KevTheKoiFishy/LMPK-362-Project/src/sd_sdcard.c

#include <stdio.h>
#include <stdlib.h>
#include <string.h>
#include <errno.h>
#include "pico/stdlib.h"

#include "sd_ff.h"
#include "sd_diskio.h"
#include "sd_sdcard.h"
#include "sd_uart.h"
#include "sd_audio.h"

#include "hardware/watchdog.h"
#include "watchdog.c"

// Just because i fw it
int _read(__unused int handle, char *buffer, int length);

FATFS fs_storage; // Global file system object
const char *month_name[] = {
    [1] = "Jan",
    [2] = "Feb",
    [3] = "Mar",
    [4] = "Apr",
    [5] = "May",
    [6] = "Jun",
    [7] = "Jul",
    [8] = "Aug",
    [9] = "Sep",
    [10] = "Oct",
    [11] = "Nov",
    [12] = "Dec",
};
typedef union {
    struct {
        unsigned int bisecond:5; // seconds divided by 2
        unsigned int minute:6;
        unsigned int hour:5;
        unsigned int day:5;
        unsigned int month:4;
        unsigned int year:7;
    };
} fattime_t;

// Current time in the FAT file system format.
static fattime_t fattime;

void set_fattime(int year, int month, int day, int hour, int minute, int second)
{
    fattime_t newtime;
    newtime.year = year - 1980;
    newtime.month = month;
    newtime.day = day;
    newtime.hour = hour;
    newtime.minute = minute;
    newtime.bisecond = second/2;
    int len = sizeof newtime;
    memcpy(&fattime, &newtime, len);
}

void advance_fattime(void)
{
    fattime_t newtime = fattime;
    newtime.bisecond += 1;
    if (newtime.bisecond == 30) {
        newtime.bisecond = 0;
        newtime.minute += 1;
    }
    if (newtime.minute == 60) {
        newtime.minute = 0;
        newtime.hour += 1;
    }
    if (newtime.hour == 24) {
        newtime.hour = 0;
        newtime.day += 1;
    }
    if (newtime.month == 2) {
        if (newtime.day >= 29) {
            int year = newtime.year + 1980;
            if ((year % 1000) == 0) { // we have a leap day in 2000
                if (newtime.day > 29) {
                    newtime.day -= 28;
                    newtime.month = 3;
                }
            } else if ((year % 100) == 0) { // no leap day in 2100
                if (newtime.day > 28)
                newtime.day -= 27;
                newtime.month = 3;
            } else if ((year % 4) == 0) { // leap day for other mod 4 years
                if (newtime.day > 29) {
                    newtime.day -= 28;
                    newtime.month = 3;
                }
            }
        }
    } else if (newtime.month == 9 || newtime.month == 4 || newtime.month == 6 || newtime.month == 10) {
        if (newtime.day == 31) {
            newtime.day -= 30;
            newtime.month += 1;
        }
    } else {
        if (newtime.day == 0) { // cannot advance to 32
            newtime.day = 1;
            newtime.month += 1;
        }
    }
    if (newtime.month == 13) {
        newtime.month = 1;
        newtime.year += 1;
    }

    fattime = newtime;
}

uint32_t get_fattime(void)
{
    union FattimeUnion {
        fattime_t time;
        uint32_t value;
    };

    union FattimeUnion u;
    u.time = fattime;
    return u.value;
}

int to_int(char *start, char *end, int base)
{
    int n = 0;
    for( ; start != end; start++)
        n = n * base + (*start - '0');
    return n;
}

void print_error(FRESULT fr, const char *msg)
{
    const char *errs[] = {
            [FR_OK] = "Success",
            [FR_DISK_ERR] = "Hard error in low-level disk I/O layer",
            [FR_INT_ERR] = "Assertion failed",
            [FR_NOT_READY] = "Physical drive cannot work",
            [FR_NO_FILE] = "File not found",
            [FR_NO_PATH] = "Path not found",
            [FR_INVALID_NAME] = "Path name format invalid",
            [FR_DENIED] = "Permision denied",
            [FR_EXIST] = "Prohibited access",
            [FR_INVALID_OBJECT] = "File or directory object invalid",
            [FR_WRITE_PROTECTED] = "Physical drive is write-protected",
            [FR_INVALID_DRIVE] = "Logical drive number is invalid",
            [FR_NOT_ENABLED] = "Volume has no work area",
            [FR_NO_FILESYSTEM] = "Not a valid FAT volume",
            [FR_MKFS_ABORTED] = "f_mkfs aborted",
            [FR_TIMEOUT] = "Unable to obtain grant for object",
            [FR_LOCKED] = "File locked",
            [FR_NOT_ENOUGH_CORE] = "File name is too large",
            [FR_TOO_MANY_OPEN_FILES] = "Too many open files",
            [FR_INVALID_PARAMETER] = "Invalid parameter",
    };
    if (fr < 0 || fr >= sizeof errs / sizeof errs[0])
        printf("%s: Invalid error\n", msg);
    else
        printf("%s: %s\n", msg, errs[fr]);
}

void date(int argc, char *argv[])
{
    if (argc == 2) {
        char *d = argv[1];
        if (strlen(d) != 14) {
            printf("Date format: YYYYMMDDHHMMSS\n");
            return;
        }
        for(int i=0; i<14; i++)
            if (d[i] < '0' || d[i] > '9') {
                printf("Date format: YYYMMDDHHMMSS\n");
                return;
            }
        int year = to_int(d, &d[4], 10);
        int month = to_int(&d[4], &d[6], 10);
        int day   = to_int(&d[6], &d[8], 10);
        int hour  = to_int(&d[8], &d[10], 10);
        int minute = to_int(&d[10], &d[12], 10);
        int second = to_int(&d[12], &d[14], 10);
        set_fattime(year, month, day, hour, minute, second);
        return;
    }
    int integer = get_fattime();
    union {
        int integer;
        fattime_t ft;
    } u;
    u.integer = integer;
    fattime_t ft = u.ft;
    int year = ft.year + 1980;
    int month = ft.month;
    printf("%d-%s-%02d %02d:%02d:%02d\n",
            year, month_name[month], ft.day, ft.hour, ft.minute, ft.bisecond*2);
}

void append(int argc, char *argv[])
{
    if (argc != 2) {
        printf("Specify only one file name to append to.");
        return;
    }
    FIL fil;        /* File object */
    char line[100]; /* Line buffer */
    FRESULT fr;     /* FatFs return code */
    fr = f_open(&fil, argv[1], FA_WRITE|FA_OPEN_EXISTING|FA_OPEN_APPEND);
    if (fr) {
        print_error(fr, argv[1]);
        return;
    }
    printf("To end append, enter a line with a single '.'\n");
    for(;;) {
        // fgets(line, sizeof(line)-1, stdin);
        _read(0, line, sizeof(line)-1);
        if (line[0] == '.' && (line[1] == '\n' || (line[1] == '\r' && line[2] == '\n')))
            break;
        int len = strlen(line);
        if (line[len-1] == '\004')
            len -= 1;
        UINT wlen;
        fr = f_write(&fil, (BYTE*)line, len, &wlen);
        if (fr)
            print_error(fr, argv[1]);
    }
    f_close(&fil);
}

void input(int argc, char *argv[])
{
    if (argc != 2) {
        printf("Specify only one file name to create.");
        return;
    }
    FIL fil;        /* File object */
    char line[100]; /* Line buffer */
    FRESULT fr;     /* FatFs return code */
    fr = f_open(&fil, argv[1], FA_WRITE|FA_CREATE_NEW);
    if (fr) {
        print_error(fr, argv[1]);
        return;
    }
    printf("To end input, enter a line with a single '.'\n");
    for(;;) {
        fgets(line, sizeof(line)-1, stdin);
        if (line[0] == '.' && (line[1] == '\n' || (line[1] == '\r' && line[2] == '\n')))
            break;
        int len = strlen(line);
        if (line[len-1] == '\004')
            len -= 1;
        UINT wlen;
        fr = f_write(&fil, (BYTE*)line, len, &wlen);
        if (fr)
            print_error(fr, argv[1]);
    }
    f_close(&fil);
}

void ls(int argc, char *argv[])
{
    FRESULT res;
    DIR dir;
    static FILINFO fno;
    const char *path = "";
    int info = 0;
    int i=1;
    int chk = argc > i;
    do {
        if (chk && argv[i][0] == '-') {
            for(char *c=&argv[i][1]; *c; c++)
                if (*c == 'l')
                    info=1;
            if (i+1 < argc) {
                i += 1;
                continue;
            }
        } else {
            path = argv[i];
        }

        res = f_opendir(&dir, path);                       /* Open the directory */
        if (res != FR_OK) {
            print_error(res, argv[1]);
            return;
        }
        for (;;) {
            res = f_readdir(&dir, &fno);                   /* Read a directory item */
            if (res != FR_OK || fno.fname[0] == 0) break;  /* Break on error or end of dir */
            if (info) {
                printf("%04d-%s-%02d %02d:%02d:%02d %12ld %c%c%c%c%c ",
                        (fno.fdate >> 9) + 1980,
                        month_name[fno.fdate >> 5 & 15],
                        fno.fdate & 31,
                        fno.ftime >> 11,
                        fno.ftime >> 5 & 63,
                        (fno.ftime & 31) * 2,
                        fno.fsize,
                        (fno.fattrib & AM_DIR) ? 'D' : '-',
                        (fno.fattrib & AM_RDO) ? 'R' : '-',
                        (fno.fattrib & AM_HID) ? 'H' : '-',
                        (fno.fattrib & AM_SYS) ? 'S' : '-',
                        (fno.fattrib & AM_ARC) ? 'A' : '-');
            }
            if (path[0] != '\0')
                printf("%s/%s\n", path, fno.fname);
            else
                printf("%s\n", fno.fname);
        }
        f_closedir(&dir);
        i += 1;
    } while(i<argc);
}

void mkdir(int argc, char *argv[])
{
    for(int i=1; i<argc; i++) {
        FRESULT res = f_mkdir(argv[i]);
        if (res != FR_OK) {
            print_error(res, argv[i]);
            return;
        }
    }
}

void mount(__unused int argc, __unused char *argv[])
{
    FATFS *fs = &fs_storage;
    if (fs->id != 0) {
        print_error(FR_DISK_ERR, "Already mounted.");
        return;
    }
    int res = f_mount(fs, "", 1);
    if (res != FR_OK)
        print_error(res, "Error occurred while mounting");
}

void pwd(__unused int argc, __unused char *argv[])
{
    char line[100];
    FRESULT res = f_getcwd(line, sizeof line);
    if (res != FR_OK)
        print_error(res, "pwd");
    else
        printf("%s\n", line);
}

void play_wav_print_man() {
    printf("Usage: play-wav [operation] [file_path]\n");
    printf("    operation:\n");
    printf("        play:   Start play from beginning\n");
    printf("        pause:  Pause audio\n");
    printf("        seek:   Seek to time specified\n");
    printf("        stop:   Pause audio and close file\n");
    printf("    file_path: Relative path of WAV file.\n");
}

void play_wav(int argc, char *argv[]) {
    if (argc < 2) {
        printf("Operation Not Specified.\n");
        play_wav_print_man();
        return;
    }

    if (!strcmp(argv[1], "play")){
        if (argc < 3) {
            printf("Filepath Not Specified.\n");
            play_wav_print_man();
            return;
        }
        char * file_path = argv[2];
        audio_play_sequence(file_path);
    } else if (!strcmp(argv[1], "stop")){
        stop_audio_playback();
        close_sd_audio_file();
    } else {
        printf("Operation \"%s\" not supported.\n", argv[1]);
        play_wav_print_man();
        return;
    }
}

void rm(int argc, char *argv[])
{
    FRESULT res;
    for(int i=1; i<argc; i++) {
        res = f_unlink(argv[i]);
        if (res != FR_OK)
            print_error(res, argv[i]);
    }
}

void cat(int argc, char *argv[])
{
    for(int i=1; i<argc; i++) {
        FIL fil;        /* File object */
        char line[100]; /* Line buffer */
        FRESULT fr;     /* FatFs return code */

        /* Open a text file */
        fr = f_open(&fil, argv[i], FA_READ);
        if (fr) {
            print_error(fr, argv[i]);
            return;
        }

        /* Read every line and display it */
        while(f_gets(line, sizeof line, &fil))
            printf(line);
        /* Close the file */
        f_close(&fil);
    }
}

void cat_hex(int argc, char *argv[]) {
    if (argc < 2) { return; }

    errno = 0; char * endptr;
    uint num_lines_log = strtol(argv[1], &endptr, 10);
    if (errno) { printf("cat_hex: Could not convert num_lines_log argument to int."); }

    for(int i=2; i<argc; i++) {
        FIL fil;        /* File object */
        FRESULT fr;     /* FatFs return code */
        char line[16];  /* Line buffer */
        UINT rb;
        uint read_bytes = 0;
        uint lines_read = 0;

        /* Open a text file */
        if ((fr = f_open(&fil, argv[i], FA_READ))) {
            print_error(fr, argv[i]);
            return;
        }

        /* Read 16 bytes at a time and display it */
        while(!(fr = f_read(&fil, line, 16, &rb))){
            printf(   "%8d  ", lines_read);
            printf("0x%08x  ", read_bytes += rb);

            for (uint8_t ib = 0; ib < 16; ++ib){
                printf("%02x ", line[ib]);
            }
            printf("  ");
            for (uint8_t ib = 0; ib < 16; ++ib){
                char this_ch = line[ib];
                if (32 <= this_ch && this_ch <= 126) {printf("%c", this_ch);} else if (this_ch == 0) {printf(" ");} else {printf(".");}
                if ((ib & 0x3) == 0b11) { printf(" "); }
            }
            printf("\n");

            if (++lines_read > num_lines_log) { break; }
        }
        /* Close the file */
        f_close(&fil);
    }
}

void cd(int argc, char *argv[])
{
    if (argc > 2) {
        printf("Too many arguments.");
        return;
    }
    FRESULT res;
    if (argc == 1) {
        res = f_chdir("/");
        if (res)
            print_error(res, "(default path)");
        return;
    }
    res = f_chdir(argv[1]);
    if (res)
        print_error(res, argv[1]);
}

void restart(__unused int argc, __unused char *argv[])
{
    printf("Restarting microcontroller...\n\n\n");
    sleep_ms(100); // wait for message to be sent
    watchdog_reboot(0, 0, 0);
}

bool sd_uart_block = true;
bool sd_cli_running(void) {
    return sd_uart_block;
}
void exit_cli(__unused int argc, __unused char *argv[]){
    printf("End SD-UART CLI.\n\n");
    sd_uart_block = false;
}
