KevTheKoiFishy/LMPK-362-Project/include/time.h

#include    <hardware/timer.h>
#include    <pico/time.h>

#include    "time_utils.h"

#define     TIME_ZONE_OFFSET    -5   // EST
#define     DAYLIGHT_SAVINGS_EN false

void        dst_enable()                    ;
void        dst_disable()                   ;
void        alarm_enable()                  ;
void        alarm_disable()                 ;
void        set_alarm_time (my_alarm_t time);
void        set_time_zone  (int8_t offset)  ;
my_alarm_t  get_alarm_cfg()                 ;
`
my_time_t   get_utc_time()      ;
my_date_t   get_utc_date()      ;
my_time_t   get_local_std_time();
my_date_t   get_local_std_date();
my_time_t   get_local_dst_time(); 
my_date_t   get_local_dst_date();
my_time_t   get_local_time()    ;
my_date_t   get_local_date()    ;

// bool        time_update_isr(__unused struct repeating_timer *t);
void        time_update_isr();
void        config_time_update_int();
void        alarm_fire_routine();
